lyso1/LCK75/LCK75 images/mainboard.png

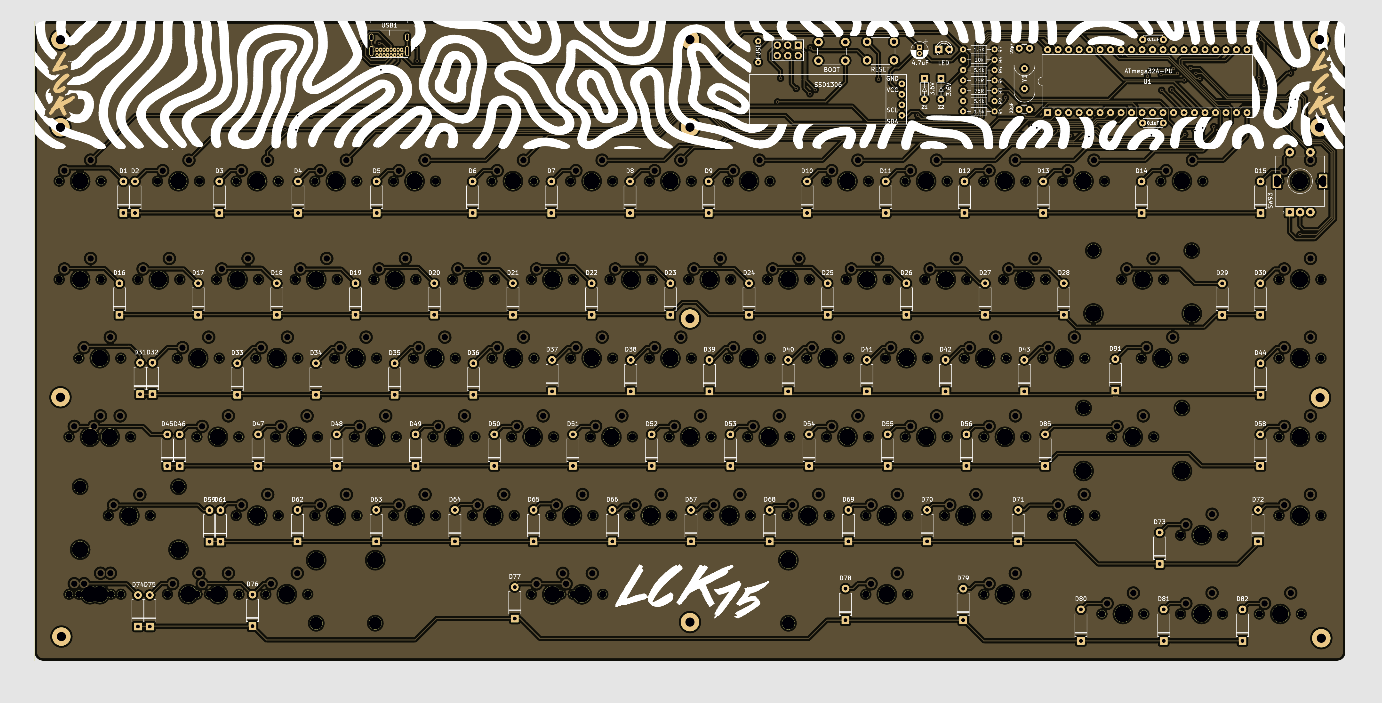
LCK75 images/mainboard.png
